dimchickka/gyroscope_final_project/gyroscope_fw/Src/Timers.c

#include "Timers.h"


void MX_TIM2_Init(void){
  //Тактируется от 64МГц
  //Таймер переполняется каждые 10 мс
  TIM_ClockConfigTypeDef sClockSourceConfig = {0};
  TIM_MasterConfigTypeDef sMasterConfig = {0};

  htim2.Instance = TIM2;
  htim2.Init.Prescaler = 63999;
  htim2.Init.CounterMode = TIM_COUNTERMODE_UP;
  htim2.Init.Period = 99;
  htim2.Init.ClockDivision = TIM_CLOCKDIVISION_DIV1;
  htim2.Init.AutoReloadPreload = TIM_AUTORELOAD_PRELOAD_DISABLE;
  
  if (HAL_TIM_Base_Init(&htim2) != HAL_OK)
  {
    Error_Handler();
  }
  sClockSourceConfig.ClockSource = TIM_CLOCKSOURCE_INTERNAL;
  
  if (HAL_TIM_ConfigClockSource(&htim2, &sClockSourceConfig) != HAL_OK){
    Error_Handler();
  }
  sMasterConfig.MasterOutputTrigger = TIM_TRGO_RESET;
  sMasterConfig.MasterSlaveMode = TIM_MASTERSLAVEMODE_DISABLE;
  
  if (HAL_TIMEx_MasterConfigSynchronization(&htim2, &sMasterConfig) != HAL_OK){
    Error_Handler();
  }
}
